brandonheller/skydelta/effector_flange.scad

// Effector Flange attachment
// This part shares dimensions with effector.scad in Johann's Kossel repo:
// git://github.com/jcrocholl/kossel.git

include <config.scad>;
include <effector_tube.scad>;

flange_height = 4;
tube_surround_r = effector_tube_or + 1.5;
main_height = 20;
rib_width = 2;

module effector_flange() {
	difference() {
		intersection() {
			union() {
				// Main body
				cylinder(r=effector_body_r, h=flange_height, $fn=64);
				// Center solid tunnel
				cylinder(r=tube_surround_r, h=main_height, $fn=64);
				// "Ribs"
				for (a = [0:60:359]) rotate([0, 0, 30+a]) {
	 				translate([-rib_width/2, 0, -delta]) cube([rib_width, effector_body_r, main_height+2*delta], $fn=24);
	  			}
			}
			// Outer cone shape to trim ribs
			cylinder(r1=effector_body_r+2, r2=tube_surround_r, h=main_height, $fn=64);
			// Restrict to the main body cylinder
			cylinder(r=effector_body_r, h=main_height, $fn=128);
		}
		// Center hole for grabbing tube
		translate([0, 0, -delta]) cylinder(r=effector_tube_or, h=main_height+2*delta, $fn=64);
		// Mounting holes
		for (a = [0:60:359]) rotate([0, 0, a]) {
	 		translate([0, mount_radius, -delta]) cylinder(r=m3_r, h=flange_height+2*delta, $fn=24);
	  	}
	}
}

//effector_flange();
