brandonheller/skydelta/filament_assembly.scad

include <bearing_holder.scad>;
include <idler_mount.scad>;
include <config.scad>;

module idler_assembly() {
	translate([length/2, 0, bearing_base_thickness+flange_height]) {
		color(color) bearing_holder();
		translate([0, 0, bearing_608_h]) idler_mount_assembly_double();
		translate([0, 0, 100]) rotate([180, 0, 0]) color(color) bearing_holder();
	}
}

//idler_assembly();
